Cippppy/SmartHomeLockbox/Drivers/I2C.c

/**
 * I2C.c
 *  This file is based off the TI Resource named, "msp430fr235x_eusci_i2c_standard_master.c"
 *  It uses the functions inside the resource to try and make i2c work for this project.
 *      author: Christian Cipolletta
 *      version: 5/5/2023
 */

#include <msp430.h>
#include <stdint.h>
#include <stdbool.h>
#include "I2C.h"
#include "Adafruit_BME280.h"

/* Used to track the state of the software state machine*/
I2C_Mode MasterMode = IDLE_MODE;

/* The Register Address/Command to use*/
uint8_t TransmitRegAddr = 0;

/* ReceiveBuffer: Buffer used to receive data in the ISR
 * RXByteCtr: Number of bytes left to receive
 * ReceiveIndex: The index of the next byte to be received in ReceiveBuffer
 * TransmitBuffer: Buffer used to transmit data in the ISR
 * TXByteCtr: Number of bytes left to transfer
 * TransmitIndex: The index of the next byte to be transmitted in TransmitBuffer
 * */
uint8_t ReceiveBuffer[MAX_BUFFER_SIZE] = {0};
uint8_t RXByteCtr = 0;
uint8_t ReceiveIndex = 0;
uint8_t TransmitBuffer[MAX_BUFFER_SIZE] = {0};
uint8_t TXByteCtr = 0;
uint8_t TransmitIndex = 0;

/* For slave device with dev_addr, writes the data specified in *reg_data
 *
 * dev_addr: The slave device address.
 *           Example: SLAVE_ADDR
 * reg_addr: The register or command to send to the slave.
 *           Example: CMD_TYPE_0_MASTER
 * *reg_data: The buffer to write
 *           Example: MasterType0
 * count: The length of *reg_data
 *           Example: TYPE_0_LENGTH
 *  */
I2C_Mode I2CB1_Master_ReadReg(uint8_t dev_addr, uint8_t reg_addr, uint8_t count)
{
    /* Initialize state machine */
    MasterMode = TX_REG_ADDRESS_MODE;
    TransmitRegAddr = reg_addr;
    RXByteCtr = count;
    TXByteCtr = 0;
    ReceiveIndex = 0;
    TransmitIndex = 0;

    /* Initialize slave address and interrupts */
    UCB1I2CSA = dev_addr;
    UCB1IFG &= ~(UCTXIFG + UCRXIFG);       // Clear any pending interrupts
    UCB1IE &= ~UCRXIE;                       // Disable RX interrupt
    UCB1IE |= UCTXIE;                        // Enable TX interrupt

    UCB1CTLW0 |= UCTR + UCTXSTT;             // I2C TX, start condition
    __bis_SR_register(LPM0_bits + GIE);              // Enter LPM0 w/ interrupts

    return MasterMode;

}

/* For slave device with dev_addr, read the data specified in slaves reg_addr.
 * The received data is available in ReceiveBuffer
 *
 * dev_addr: The slave device address.
 *           Example: SLAVE_ADDR
 * reg_addr: The register or command to send to the slave.
 *           Example: CMD_TYPE_0_SLAVE
 * count: The length of data to read
 *           Example: TYPE_0_LENGTH
 *  */
I2C_Mode I2CB1_Master_WriteReg(uint8_t dev_addr, uint8_t reg_addr, uint8_t *reg_data, uint8_t count)
{
    /* Initialize state machine */
    MasterMode = TX_REG_ADDRESS_MODE;
    TransmitRegAddr = reg_addr;

    //Copy register data to TransmitBuffer
    CopyArray(reg_data, TransmitBuffer, count);

    TXByteCtr = count;
    RXByteCtr = 0;
    ReceiveIndex = 0;
    TransmitIndex = 0;

    /* Initialize slave address and interrupts */
    UCB1I2CSA = dev_addr;
    UCB1IFG &= ~(UCTXIFG + UCRXIFG);       // Clear any pending interrupts
    UCB1IE &= ~UCRXIE;                       // Disable RX interrupt
    UCB1IE |= UCTXIE;                        // Enable TX interrupt

    UCB1CTLW0 |= UCTR + UCTXSTT;             // I2C TX, start condition
    __bis_SR_register(LPM0_bits + GIE);              // Enter LPM0 w/ interrupts

    return MasterMode;
}

void CopyArray(uint8_t *source, uint8_t *dest, uint8_t count)
{
    uint8_t copyIndex = 0;
    for (copyIndex = 0; copyIndex < count; copyIndex++)
    {
        dest[copyIndex] = source[copyIndex];
    }
}
